Ste3py/RCN1BNCMOD/img/img_2.jpg

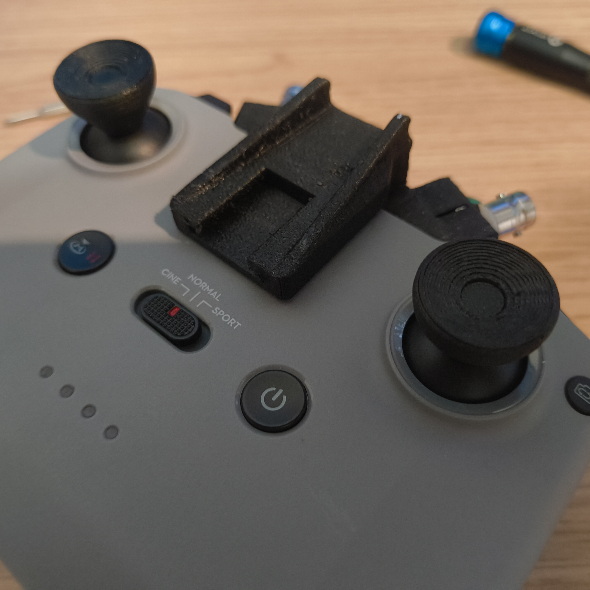
img/img_2.jpg
