Ste3py/RCN1BNCMOD/img/img_6.jpg

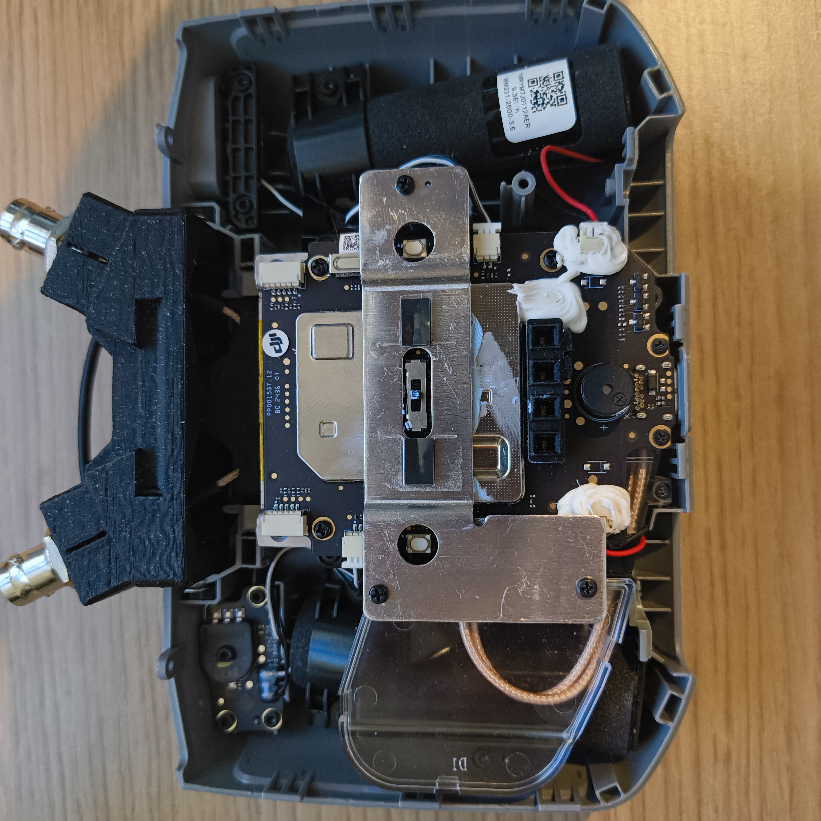
img/img_6.jpg
